SonalPinto/purple-owl/assets/photos/dark1.jpg

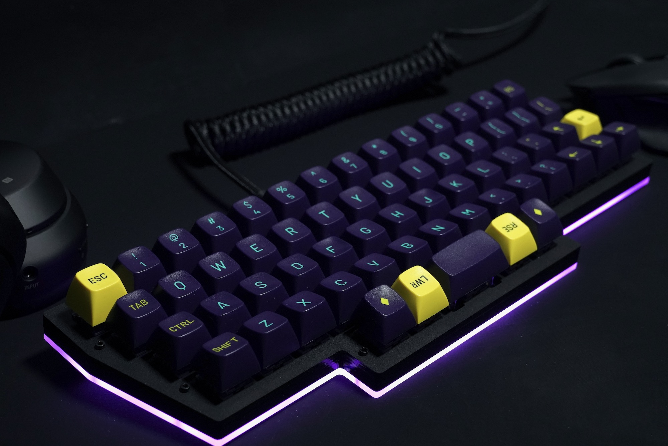
assets/photos/dark1.jpg
